Sheep26/ScholDigi/assets/c7914370-773e-47dc-8163-8aaac59b5128.PNG

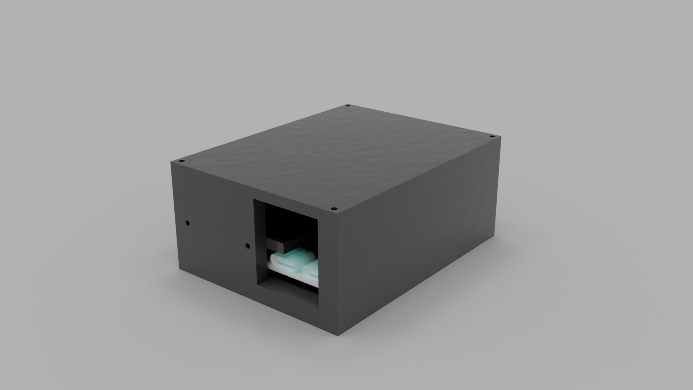
assets/c7914370-773e-47dc-8163-8aaac59b5128.PNG
