Sheep26/ScholDigi/assets/ScholDigiCase_2026-Jul-02_07-15-14AM-000_CustomizedView2563251831.png

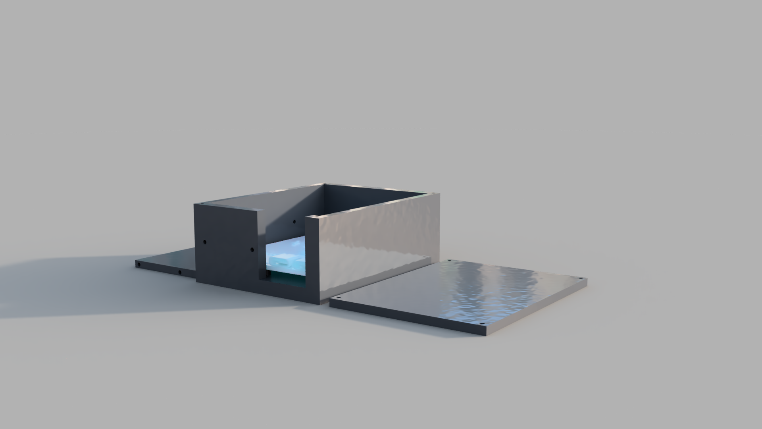
assets/ScholDigiCase_2026-Jul-02_07-15-14AM-000_CustomizedView2563251831.png
