Sheep26/ScholDigi/assets/ScholDigiCase_2026-Jul-02_07-16-00AM-000_CustomizedView41050098525.png

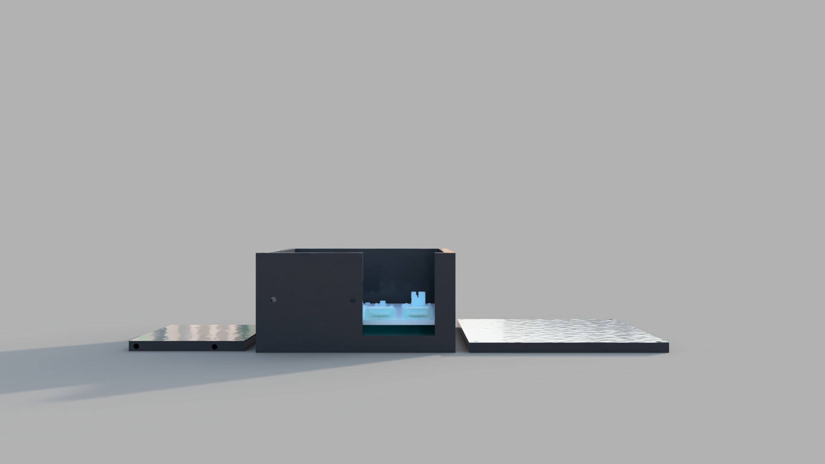
assets/ScholDigiCase_2026-Jul-02_07-16-00AM-000_CustomizedView41050098525.png
