Sheep26/ScholDigi/assets/ScholDigiCase_2026-Jul-02_07-20-28AM-000_CustomizedView37964384368.png

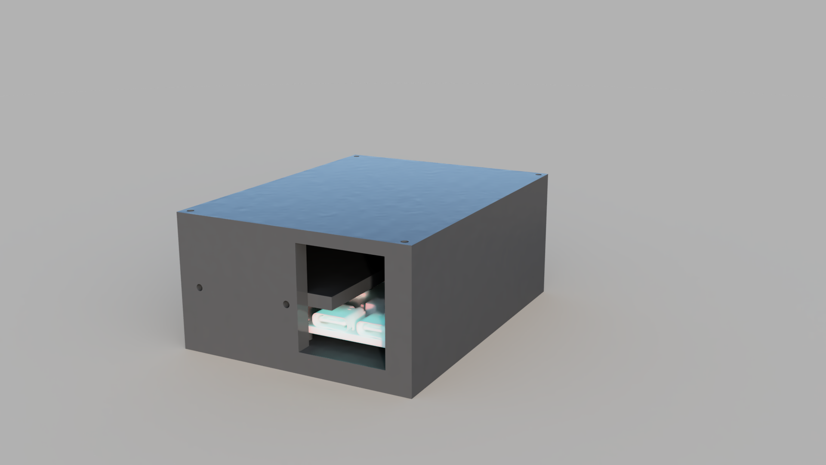
assets/ScholDigiCase_2026-Jul-02_07-20-28AM-000_CustomizedView37964384368.png
