Sheep26/ScholDigi/firmware/main/exercise.c

#include <exercise.h>

void addExercisePoint(exercise_t *exercise, exercise_point_t *point) {
    if (!exercise->list)
        exercise->list = point;

    if (exercise->last)
        exercise->last->next = point;

    exercise->last = point;
}
